jzhang0502/EEG-Individual-Project/Schematics/EEG_Schematic_LT.asc

C1: cap; 0.1µ
C2: cap; 33n
C3: cap; 5.6n
C4: cap; 5.6n
C7: cap; 0.033µ
C8: cap; 0.0056µ
D1: diode
D2: diode
D3: diode
D4: diode
Electrode1: signal; SINE(0 20u 15); AC 20u
Electrode2: signal; SINE(0 0u 0); AC 0u
R1: res; 25k
R2: res; 25k
R3: res; 40k
R4: res; 40k
R5: res; 40k
R6: res; 40k
R7: res; 100k
R8: res; 1.8k
R9: res; 4.99k
R10: res; 5.6k
R11: res; 22k
R12: res; 22k
R13: res; 10k
R14: res; 499k
R15: res; 10k
R16: res; 10k
R17: res; 10k
R18: res; 2.37k
R19: res; 3300k
R20: res; 2.37k
R21: res; 10k
R22: res; 4.99k
R23: res; 2.37k
R24: res; 100k
R25: res; 5.6k
R26: res; 10k
R27: res; 10k
R28: res; 100k
R29: res; 4.99k
Rg: res; 2.37k
RightLegElectrode: signal; SINE(0 0.1 50); AC 0.1
U1: OP07
U2: OP07
U3: OP07
U4: OP07
U6: OP07
U7: OP227
U8: OP227
U9: OP07
U10: OP07
U11: OP07
U12: OP07
V1: voltage; 9
V2: voltage; 9
Named nets: 0, Vcc, Vee
INA819 Instrumentation Amplifier
G1 = 22.10
Sim G1 = 23.2
Non-inverting Op Amp
G2 = 56.56
Sim G2 = 53.99
Voltage Source 2x 9V Batteries
Inverting Op Amp
G3 = -17.86
Sim G3 = -17.88
Current total gain = 22322.82
-100uV ~ +100uV after gain = 4.4646Vpp < 5Vpp
 
Sim total gain = 22395.92
-100uV ~ +100uV after gain = 4.4792Vpp
Capacitor acts as active low-pass filter 
for fc = 1/(2*pi*C*100k) = 48.2288Hz
Common mode rejection is improved by a factor of (1 + A). 
This means a higher gain will improve the circuit"s CMRR, 
as long as there are no stability issues caused by relatively 
high gains.
Driven Right Leg Inverting Op Amp
G = -49.9
Buffer op amp provides low-impedance
connection to right leg electrode.
;ac dec 100 1m 50k
.tran 0 0.5 0
Rg determines gain of instrumentation 
amplifier INA819. A = 1 + 50k/Rg
Optional high-pass filter that connects Rref and the 
output of the instrumentation amplifier. Connect U6's
output with R6 instead of ground. Different C1 value
will affect offset of INA819.
Inverting Summing Amplifier
G4 = -1
Offset = 2.4969V
Sim offset = 2.4969
Non-inverting Op Amp
G3 = 18.86
Sim G3 = 18.88
Non-inverting summing amplifier is not a preferable choice since it will introduce
gain>1 into the system (Av = 1 + Rf/Ri, and Rf/Ri cannot be 0). The system only 
requires an offset of approximately 2.5V with gain=1. Inverting summing amplifiers
can do the job, but requires an additional inverter op amp to bound the signal to
its acceptable range.
 
For voltage divider calculation between R18, R21, and R22, check out 
https://www.electronics-tutorials.ws/opamp/opamp_4.html
For easy swapping when editing
Inverting Op Amp
G4 = -1
RFI Filter
Fc = 445.4578Hz
ESD Protection Circuit
