jzhang0502/EEG-Individual-Project/Schematics/KiCad_Project_EEG_Design/EEG_Design.kicad_sch

## KiCad design Schematics/KiCad_Project_EEG_Design/EEG_Design.kicad_sch (2024-01-09)

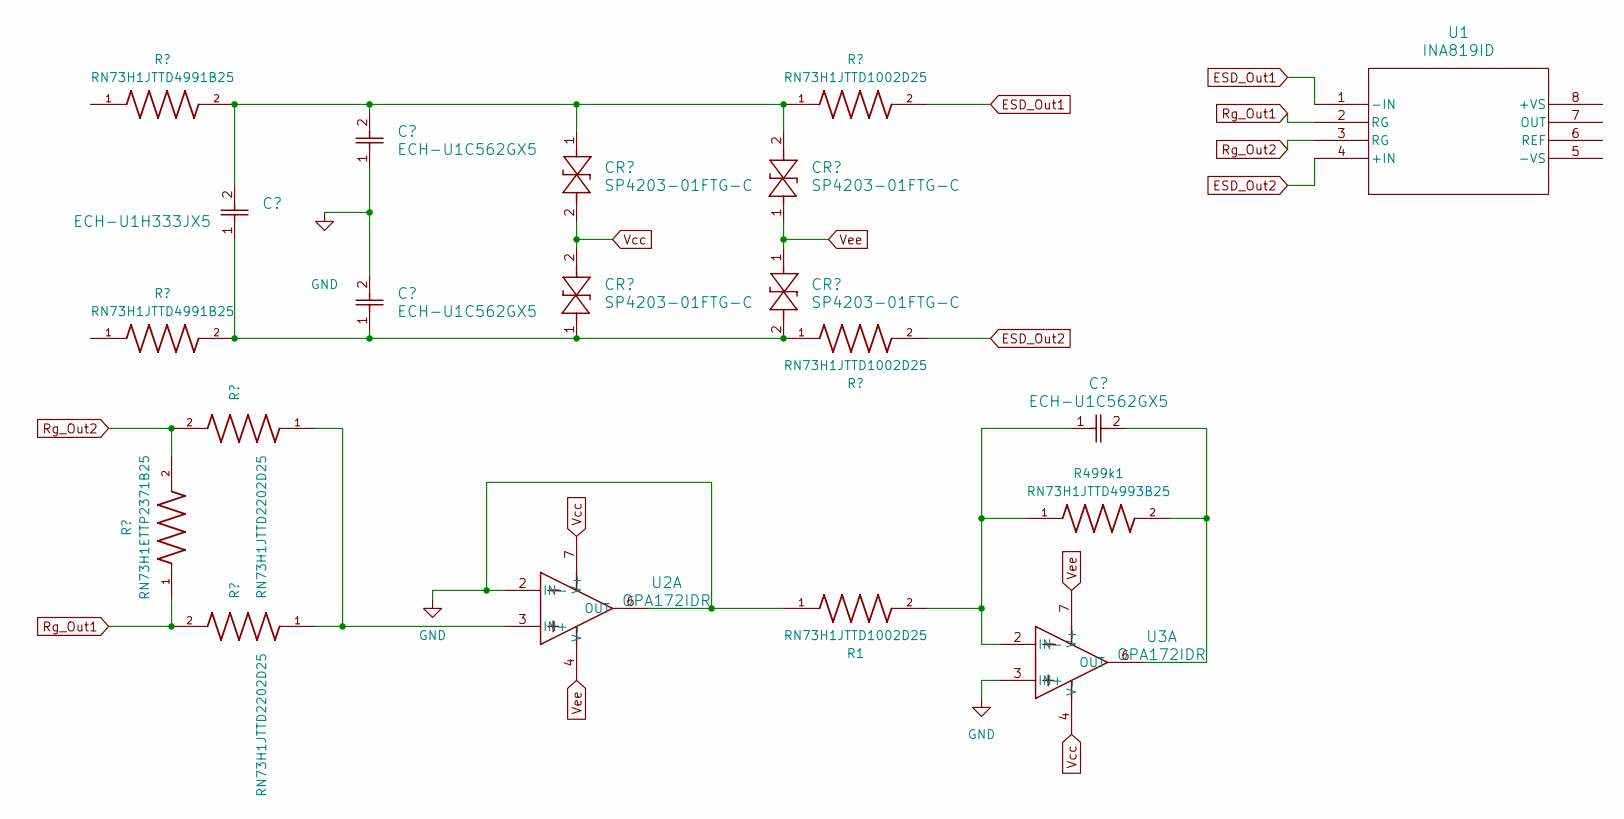
[picture p2: schematic EEG_Design.kicad_sch]

Parts:
R1: RN73H1JTTD1002D25; RESC1608X55N
R499k1: RN73H1JTTD4993B25; RESC1608X55N
U1: INA819ID; D8_TEX
U2, U3: OPA172IDR; D0008A_N

Connections:
ESD_Out1: U1.1 (-IN)
ESD_Out2: U1.4 (+IN)
GND: R1.1, U2.2 (IN-), U2.6 (OUT), U3.3 (IN+)
unnamed: R1.2, R499k1.1, U3.2 (IN-)
unnamed: R499k1.2, U3.6 (OUT)
Rg_Out1: U1.2 (RG)
Rg_Out2: U1.3 (RG)
Vcc: U2.7 (V+), U3.4 (V-)
Vee: U2.4 (V-), U3.7 (V+)
